joshua-classen/heliostat/bilder/motor/20150522_195006.jpg

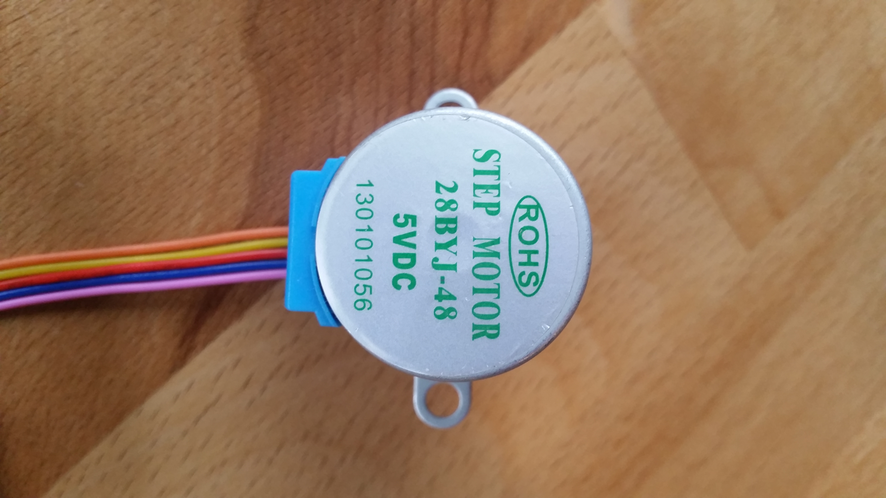
bilder/motor/20150522_195006.jpg
