joshua-classen/heliostat/bilder/motor/20150522_195052.jpg

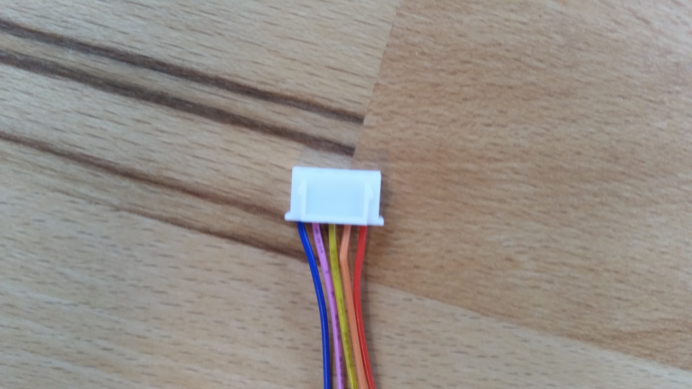
bilder/motor/20150522_195052.jpg
