joshua-classen/heliostat/bilder/motor/20150522_195122.jpg

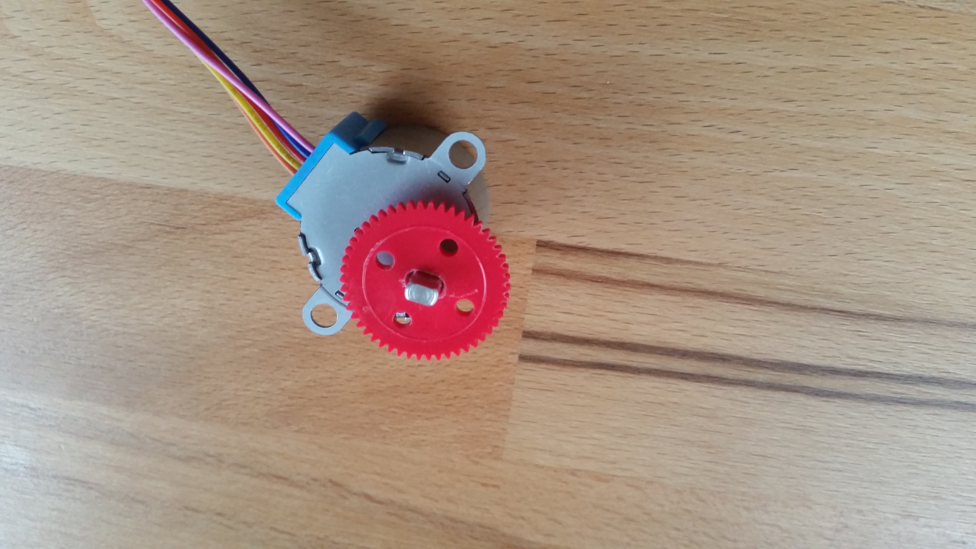
bilder/motor/20150522_195122.jpg
